terryzhw/esp32-rep-tracker/arduino_firmware/src/model.h

#ifndef MODEL_H
#define MODEL_H

// Normalization params (min/max per feature: roll, pitch)
static constexpr float NORM_MIN[] = {-186.4700f, -42.5400f};
static constexpr float NORM_MAX[] = {182.7900f, 14.4700f};
static constexpr int MODEL_WINDOW_SIZE = 50;

static const float WEIGHT0[] = {
  -0.429497f, -1.081888f, 0.142878f, 0.614045f, 1.012826f, 0.108068f, -0.197885f, 0.004681f, 
  -0.905804f, 0.895357f, 0.485917f, -0.182016f, -0.131708f, 0.827159f, 0.944690f, -0.312450f, 
  0.070049f, 0.270276f, 0.288411f, 0.220682f, -0.128280f, -0.069962f, -0.143791f, 0.125104f, 
  0.095188f, 0.140155f, 0.120540f, -0.175452f, -0.044443f, -0.183247f, -0.185254f, -0.135934f, 
  0.157218f, -1.208014f, -0.407286f, 0.275884f, 0.637745f, 0.000940f, 0.165335f, 0.117446f, 
  -0.346992f, 0.713667f, 0.678834f, -0.181038f, 0.120350f, 0.686859f, 0.522790f, -0.149807f, 
  0.172888f, 0.137952f, 0.001745f, 0.061210f, -0.090538f, 0.162309f, -0.045787f, 0.035492f, 
  0.226398f, 0.090703f, -0.143344f, 0.050893f, 0.044971f, 0.024256f, -0.128072f, 0.232590f, 
  0.048170f, -0.865535f, -0.217620f, -0.108862f, 0.854005f, -0.173611f, 0.190603f, 0.031673f, 
  -0.426036f, 0.663713f, 0.181047f, 0.190581f, -0.047619f, 0.383311f, 0.764119f, -0.101092f, 
  0.232555f, 0.056411f, 0.048029f, -0.050875f, -0.146657f, -0.211437f, 0.113383f, -0.109490f, 
  0.191068f, 0.033442f, 0.184380f, 0.128500f, -0.168622f, 0.014334f, 0.252082f, -0.117939f, 
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
  0.078142f, -0.658565f, -1.458821f, -1.074028f, -0.053879f, 0.878579f, 0.717542f, -1.226026f, 
  0.056264f, 0.241631f, -0.378097f, -0.305531f, 0.322401f, -0.054563f, 0.682634f, -0.685089f, 
  -0.315783f, 0.304386f, 0.060904f, -0.094954f, 0.697087f, 0.127120f, -0.065305f, 0.157509f, 

};

static const float BIAS1[] = {
  0.309195f, 0.429314f, 0.343715f, 0.333575f, -0.355080f, -0.412011f, -0.383536f, 0.410551f, 

};

static const float WEIGHT2[] = {
  -0.525540f, -2.278097f, -1.270433f, -1.077075f, 0.696423f, 0.337534f, 0.410623f, -1.564264f, 

};

static const float BIAS2[] = {
  -0.338230f, 
};

#endif // MODEL_H
