terryzhw/esp32-rep-tracker/esp-idf-firmware/main/model.h

#ifndef MODEL_H
#define MODEL_H

// Normalization params (min/max per feature: roll, pitch)
static const float NORM_MIN[] = {-84.6800f, -17.2500f};
static const float NORM_MAX[] = {78.9000f, 58.7900f};
#define MODEL_WINDOW_SIZE 50

static const float WEIGHT0[] = {
  -0.415974f, 0.087729f, -0.377692f, -0.497152f, -0.004155f, -0.564614f, 0.034721f, -0.337535f, 
  -0.345590f, -0.102707f, 0.328946f, 0.074536f, -0.212868f, 0.150497f, 0.166197f, -0.089623f, 
  -0.261859f, -0.179629f, 0.120000f, -0.480111f, -0.180745f, -0.055152f, -0.155002f, -0.117196f, 
  -0.113081f, 0.138993f, -0.138375f, 0.143825f, 0.001055f, 0.210738f, -0.089081f, -0.133681f, 
  -0.149632f, -0.086648f, -0.593105f, -0.457642f, -0.003952f, -0.272125f, -0.061922f, -0.166533f, 
  -0.245164f, -0.129767f, 0.202062f, -0.031518f, 0.122699f, 0.089376f, 0.059740f, 0.132710f, 
  0.021706f, -0.183825f, -0.018422f, -0.220806f, -0.099270f, 0.050757f, -0.035548f, -0.331775f, 
  0.116630f, -0.014200f, 0.168248f, -0.198616f, -0.090029f, -0.156490f, -0.096189f, 0.080959f, 
  -0.079082f, -0.091040f, -0.434308f, -0.403980f, -0.005248f, -0.390963f, 0.276595f, -0.023294f, 
  -0.074911f, -0.064165f, 0.040722f, 0.098921f, 0.038153f, -0.041030f, 0.073980f, -0.137227f, 
  0.035828f, -0.151101f, 0.108923f, -0.467019f, 0.002061f, -0.255717f, -0.290387f, 0.122194f, 
  -0.022271f, 0.188593f, -0.023399f, 0.129604f, 0.076277f, 0.129981f, -0.111898f, -0.153667f, 
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
  -0.304544f, 0.064480f, -0.360262f, -0.251399f, -0.348433f, -0.405678f, -0.035987f, -0.492075f, 
  -0.399035f, -0.746329f, 1.220548f, 0.728965f, -1.113299f, 1.295580f, 0.269639f, 1.013956f, 
  -0.101550f, -0.418348f, -0.113633f, 0.382354f, -0.047566f, 0.354384f, -0.225056f, -0.446828f, 

};

static const float BIAS1[] = {
  -0.088788f, 0.176739f, -0.162171f, 0.080894f, 0.193940f, -0.090237f, 0.042090f, -0.139058f, 

};

static const float WEIGHT2[] = {
  0.694878f, -1.049752f, 0.936504f, 0.873993f, -1.173780f, 1.619769f, -0.225926f, 1.508579f, 

};

static const float BIAS2[] = {
  -0.164024f, 
};

#endif // MODEL_H
